makmorit/RMWiFiController/ControllerBoard/ControllerBoard.X/sources/process.c

#include "common.h"
#include "device.h"
#include "lcd.h"
#include "rotenc.h"
#include "process.h"
#include "manualmode.h"
#include "uart.h"
#include "timer0.h"

//
// 基板上のボタン押下時の処理
//
static void process_on_BUTTON_0()
{
}

static void process_on_BUTTON_1()
{
}

static void process_on_BUTTON_2()
{
    // 手動モードに遷移
    process_init();
}

static void process_on_BUTTON_3()
{
    // 手動モード時
    if (main_mode == 0) {
        // 正転／反転の切替
        reverse_on_manual_mode();
        return;
    }
}

static void send_uart_command(unsigned char c)
{
    // ボタン押下時に、UARTコマンドを送信する
    printf("%c\r\n", c);
}

static int process_on_button_press()
{
    int ret = 1;

    // スイッチOnに対する処理を実行
    if (BUTTON_0 == 1) {
        process_on_BUTTON_0();
        send_uart_command('A');

    } else if (BUTTON_1 == 1) {
        process_on_BUTTON_1();
        send_uart_command('M');

    } else if (BUTTON_2 == 1) {
        process_on_BUTTON_2();
        send_uart_command('E');

    } else if (BUTTON_3 == 1) {
        process_on_BUTTON_3();
        send_uart_command('C');

    } else {
        ret = 0;
    }
    return ret;
}

//
// UARTリモコンコマンド受信時の処理
//
static void process_on_uart_command(unsigned char c)
{
    switch (c) {
    case 'A':
        // 自動運転実行
        process_on_BUTTON_0();
        break;
    case 'M':
        // モード変更実行
        process_on_BUTTON_1();
        break;
    case 'E':
        // キャンセル実行
        process_on_BUTTON_2();
        break;
    case 'C':
        // 正／逆転切替実行
        process_on_BUTTON_3();
        break;
    default:
        // 無効
        break;
    }
}

//
// 入力された文字列を数値に変換
//
static unsigned char atouc(char *value)
{
    char buff[8];
    int i, n;

    // 入力された文字列を作業領域にセット
    memset(buff, 0, sizeof(buff));
    for (i = 0; value[i] != 0; i++) {
        buff[i] = value[i];
    }

    // 数値変換
    n = atoi(buff);
    if (n < 0) {
        return 0;
    } else if (255 < n) {
        return 255;
    }
    return (unsigned char)n;
}
//
// UARTに入力された内容を解析する
//
static void parse_uart_input()
{
    unsigned char c;

    unsigned char *rc_buff = get_uart_recv_buff();
    if (rc_buff == NULL) {
        return;
    }
    
    // 先頭が半角大文字以外の場合はスルー
    c = rc_buff[0];
    if (c < 64 || 90 < c) {
        return;
    }

    switch (c) {
    case 'D':
        // デューティー比入力
        c = atouc(&rc_buff[1]);
        if (rsw_counter_max < c) {
            c = rsw_counter_max;
        }
        rsw_counter_value = c;
        break;
    case 'A':
        // 自動運転実行(Auto drive)
    case 'M':
        // モード変更実行(Mode change)
    case 'E':
        // キャンセル実行(End)
    case 'C':
        // 正／逆転切替実行(direction Change)
        process_on_uart_command(c);
        break;
    default:
        // 無効
        break;
    }
}

//
// ボタン押下検知処理
//
static unsigned long btn_push_prevent_cnt;

// 割込みごとに処理（3.2768 ms）
static void switch_prevent()
{
    // カウンターが０の時は終了
    if (0 == btn_push_prevent_cnt) {
        return;
    }

    // ボタン連続押下抑止カウンターを更新
    btn_push_prevent_cnt-- ;
}

// イベントループ内の最後のステップで処理
static void switch_detection()
{
    // カウンターが０でない時は終了
    if (0 < btn_push_prevent_cnt) {
        return;
    }

    // スイッチ押下時の処理を実行
    if (process_on_button_press() != 0) {
        // 押下抑止カウンターを設定(約１秒に設定)
        btn_push_prevent_cnt = 300;
    } else {
        btn_push_prevent_cnt = 0;
    }
}

//
// センサー検知処理
//
static unsigned char reducing_sensor_flg;
static unsigned char stopping_sensor_flg;

static void process_on_REDUCING_SENSOR()
{
}

static void process_on_STOPPING_SENSOR()
{
}

// 割込みごとに処理（3.2768 ms）
static void sensor_detection()
{
    // レイアウト制御デバイス以外の場合は処理しない
    if (devide_type != DEVTYP_LAYOUT) {
        return;
    }

    // センサーOnに対する処理を実行
    if (REDUCING_SENSOR == 0) {
        reducing_sensor_flg++;
        // n回連続して検知にかかったらセンサーを踏んだと判定
        if (5 == reducing_sensor_flg) {
            process_on_REDUCING_SENSOR();
        }

    } else if (STOPPING_SENSOR == 0) {
        stopping_sensor_flg++;
        // n回連続して検知にかかったらセンサーを踏んだと判定
        if (5 == stopping_sensor_flg) {
            process_on_STOPPING_SENSOR();
        }

    } else {
        reducing_sensor_flg = 0;
        stopping_sensor_flg = 0;
    }
}

// 約 0.1 秒ごとに処理（3.2768ms × 30回）
static void process_on_100m_second()
{
    switch (main_mode) {
    case 0:
        // 手動運転モード時
        process_on_manual_mode();
        break;
    }
}

// 約 1.0 秒ごとに処理（3.2768ms × 305回）
static void process_on_one_second()
{
    switch (main_mode) {
    case 0:
        // 手動運転モード時
        process_on_one_second_manual_mode();
        break;
    }
}

// ロータリーエンコーダーの現在値変更時の処理
static void process_on_change_rotenc_val()
{
    // 値が変更時、UARTコマンドを送信する
    printf("D%u\r\n", rsw_counter_value);
}

void process_init()
{
    // 動作モードを設定
    set_device_mode();

    // ローカル変数の初期化
    btn_push_prevent_cnt = 0;
    reducing_sensor_flg = 0;
    stopping_sensor_flg = 0;

    // モードを手動モードに設定
    manual_mode_init();
}

//
// 主処理
//
void process()
{
    // UART入力を優先させる
    parse_uart_input();

    // 割込みごとに処理（3.2768 ms）
    if (tmr0_toggle == 1) {
        // ロータリーエンコーダーによる検知処理
        if (rotenc_detection() != 0) {
            process_on_change_rotenc_val();
        }
        // スイッチ連続検知抑止
        switch_prevent();
        tmr0_toggle = 0;
        // センサー検知処理
        sensor_detection();
    }

    // 約 0.1 秒ごとに処理（3.2768ms × 30回）
    if (tmr0_total_cnt_100m > 30) {
        // カウンターを初期化
        tmr0_total_cnt_100m = 0;
        // イベントごとの処理（モード／ステータス遷移）を行う
        process_on_100m_second();
    }

    // 約 1.0 秒ごとに処理（3.2768ms × 305回）
    if (tmr0_total_cnt_1s > 305) {
        // カウンターを初期化
        tmr0_total_cnt_1s = 0;
        // イベントごとの処理を行う
        process_on_one_second();
    }

    // スイッチ検知処理
    switch_detection();
}
