makmorit/RMWiFiController/AE_ESP_board/WiFiHTTPBoard/WiFiInfo.h

#ifndef __WIFIINFO_H
#define __WIFIINFO_H

#define WIFI_SSID  "RMWiFiHTTPBoard"
#define WIFI_PSWD "aab5ca713f808f5b8a8fb0b5a3df9e6b"

#define WIFI_SVR_IPADDR  "192.168.253.1"
#define WIFI_SVR_IPADDR_FN  (IPAddress(192,168,253,1))
#define WIFI_SVR_PORTNO  80

#endif // __WIFIINFO_H
