makmorit/RMWiFiController/ControllerBoard/ControllerBoard.X/sources/manualmode.h

#ifndef __MANUALMODE_H
#define __MANUALMODE_H

//
// 関数
//
void manual_mode_init();
void process_on_manual_mode();
void process_on_one_second_manual_mode();
void reverse_on_manual_mode();

#endif // __MANUALMODE_H
