makmorit/RMWiFiController/ControllerBoard/ControllerBoard.X/sources/process.h

#ifndef __PROCESS_H
#define __PROCESS_H

// モード 
//   0:手動モード・・・ダイヤルを回し、デューティー比を手動変化させるモード
//   1:自動モード（未実装）・・・EEPROMにsaveした設定値をもとに、デューティー比が自動変化するモード
//   2:プログラムモード（未実装）・・・ダイヤルを回し、自動走行用パラメーターを設定するモード
unsigned char main_mode = 0;

//
// 関数
//
void process_init();
void process();

#endif // __PROCESS_H
